Kampi/Watch-HW/production/watch-CHECKED/HTML/images/cat_png_3d_viewer_top_ZSWatch-Watch-top.png

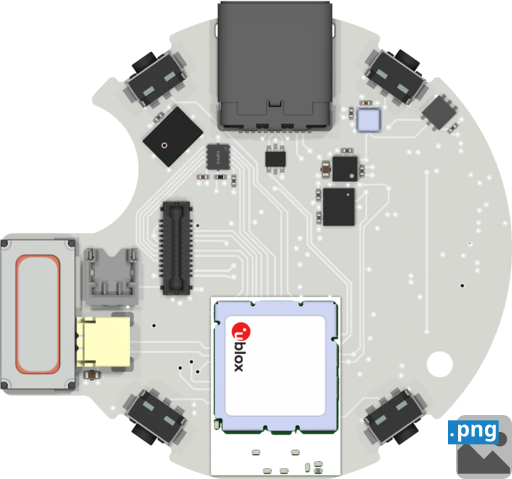
production/watch-CHECKED/HTML/images/cat_png_3d_viewer_top_ZSWatch-Watch-top.png
