Kampi/Watch-HW/production/watch-CHECKED/HTML/images/cat_pdf_assembly_ZSWatch-Watch-assembly.png

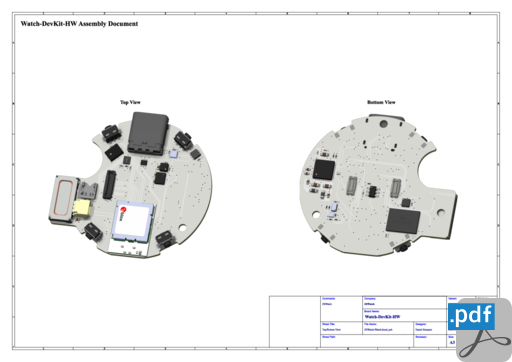
production/watch-CHECKED/HTML/images/cat_pdf_assembly_ZSWatch-Watch-assembly.png
